thomask77/nucular-keyboard/Docs/IMG_4991.JPG

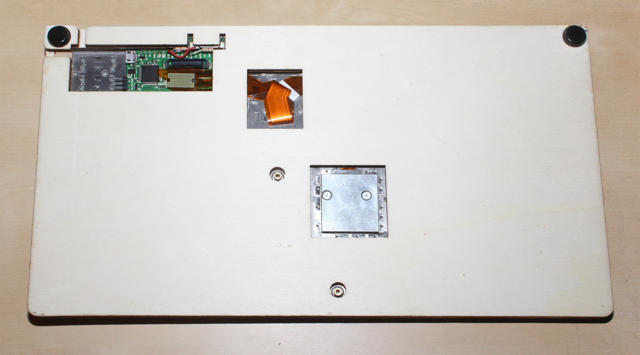
Docs/IMG_4991.JPG
