thomask77/nucular-keyboard/Docs/IMG_4995.JPG

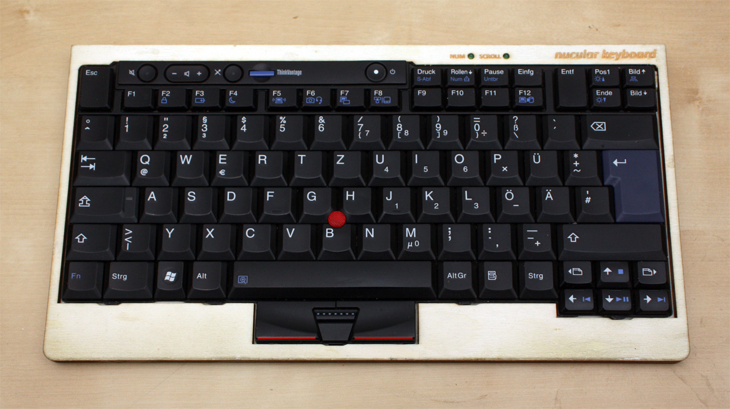
Docs/IMG_4995.JPG
