thomask77/nucular-keyboard/Bootloader/Src/main.c

/**
  ******************************************************************************
  * File Name          : main.c
  * Date               : 08/12/2014 22:01:44
  * Description        : Main program body
  ******************************************************************************
  *
  * COPYRIGHT(c) 2014 STMicroelectronics
  *
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
  ******************************************************************************
  */

/* Includes ------------------------------------------------------------------*/
#include "stm32l0xx_hal.h"
#include "usb_device.h"


/* USER CODE BEGIN 0 */

int check_boot_enter(void)
{
    uint32_t rtc_bkp0r = RTC->BKP0R;

    // clear signature
    //
    RCC->APB1ENR |=  RCC_APB1ENR_PWREN;
    PWR->CR |= PWR_CR_DBP;
    RTC->BKP0R = 0x00000000;
    PWR->CR &= ~PWR_CR_DBP;

    return (rtc_bkp0r == 0xB00710AD) ||
           (!(GPIOC->IDR & GPIO_PIN_14) &&
            !(GPIOB->IDR & GPIO_PIN_9 )  );
}

/* USER CODE END 0 */

void SystemClock_Config(void);
static void MX_GPIO_Init(void);

int main(void)
{

  /* MCU Configuration----------------------------------------------------------*/

  /* Reset of all peripherals, Initializes the Flash interface and the Systick. */
  HAL_Init();

  /* Configure the system clock */
  SystemClock_Config();

  /* System interrupt init*/
  HAL_NVIC_SetPriority(SysTick_IRQn, 0, 0);

  /* Initialize all configured peripherals */
  MX_GPIO_Init();
  MX_USB_DEVICE_Init();

  /* USER CODE BEGIN 2 */

  if (!check_boot_enter())
  {
    void (*JumpToApplication)(void);
    uint32_t JumpAddress;

    /* Test if user code is programmed starting from address 0x08004000 */
    if (((*(__IO uint32_t*)USBD_DFU_APP_DEFAULT_ADD) & 0x2FFE0000 ) == 0x20000000)
    {
      /* Jump to user application */
      JumpAddress = *(__IO uint32_t*) (USBD_DFU_APP_DEFAULT_ADD + 4);
      JumpToApplication = (void*)JumpAddress;

      /* Initialize user application's Stack Pointer */
      __set_MSP(*(__IO uint32_t*) USBD_DFU_APP_DEFAULT_ADD);
      JumpToApplication();
    }
  }

  /* USER CODE END 2 */

  /* USER CODE BEGIN 3 */
  /* Infinite loop */
  while (1)
  {

  }
  /* USER CODE END 3 */

}

/** System Clock Configuration
*/
void SystemClock_Config(void)
{

  RCC_CRSInitTypeDef RCC_CRSInitStruct;
  RCC_ClkInitTypeDef RCC_ClkInitStruct;
  RCC_PeriphCLKInitTypeDef PeriphClkInit;
  RCC_OscInitTypeDef RCC_OscInitStruct;

  __PWR_CLK_ENABLE();

  __HAL_PWR_VOLTAGESCALING_CONFIG(PWR_REGULATOR_VOLTAGE_SCALE1);

  RCC_OscInitStruct.OscillatorType = RCC_OSCILLATORTYPE_HSI|RCC_OSCILLATORTYPE_HSI48;
  RCC_OscInitStruct.HSIState = RCC_HSI_ON;
  RCC_OscInitStruct.HSICalibrationValue = 16;
  RCC_OscInitStruct.HSI48State = RCC_HSI48_ON;
  RCC_OscInitStruct.PLL.PLLState = RCC_PLL_ON;
  RCC_OscInitStruct.PLL.PLLSource = RCC_PLLSOURCE_HSI;
  RCC_OscInitStruct.PLL.PLLMUL = RCC_PLLMUL_4;
  RCC_OscInitStruct.PLL.PLLDIV = RCC_PLLDIV_2;
  HAL_RCC_OscConfig(&RCC_OscInitStruct);

  RCC_ClkInitStruct.ClockType = RCC_CLOCKTYPE_SYSCLK;
  RCC_ClkInitStruct.SYSCLKSource = RCC_SYSCLKSOURCE_PLLCLK;
  RCC_ClkInitStruct.AHBCLKDivider = RCC_SYSCLK_DIV1;
  RCC_ClkInitStruct.APB1CLKDivider = RCC_HCLK_DIV1;
  RCC_ClkInitStruct.APB2CLKDivider = RCC_HCLK_DIV1;
  HAL_RCC_ClockConfig(&RCC_ClkInitStruct, FLASH_LATENCY_1);

  PeriphClkInit.PeriphClockSelection = RCC_PERIPHCLK_USB;
  PeriphClkInit.UsbClockSelection = RCC_USBCLKSOURCE_HSI48;
  HAL_RCCEx_PeriphCLKConfig(&PeriphClkInit);

  __SYSCFG_CLK_ENABLE();

  __CRS_CLK_ENABLE();

  RCC_CRSInitStruct.Prescaler = RCC_CRS_SYNC_DIV1;
  RCC_CRSInitStruct.Source = RCC_CRS_SYNC_SOURCE_USB;
  RCC_CRSInitStruct.Polarity = RCC_CRS_SYNC_POLARITY_RISING;
  RCC_CRSInitStruct.ReloadValue = __HAL_RCC_CRS_CALCULATE_RELOADVALUE(48000000,1000);
  RCC_CRSInitStruct.ErrorLimitValue = 34;
  RCC_CRSInitStruct.HSI48CalibrationValue = 32;
  HAL_RCCEx_CRSConfig(&RCC_CRSInitStruct);

}

/** Configure pins as 
        * Analog 
        * Input 
        * Output
        * EVENT_OUT
        * EXTI
*/
void MX_GPIO_Init(void)
{

  GPIO_InitTypeDef GPIO_InitStruct;

  /* GPIO Ports Clock Enable */
  __GPIOC_CLK_ENABLE();
  __GPIOA_CLK_ENABLE();
  __GPIOB_CLK_ENABLE();

  /*Configure GPIO pin : PC14 */
  GPIO_InitStruct.Pin = GPIO_PIN_14;
  GPIO_InitStruct.Mode = GPIO_MODE_INPUT;
  GPIO_InitStruct.Pull = GPIO_PULLUP;
  HAL_GPIO_Init(GPIOC, &GPIO_InitStruct);

  /*Configure GPIO pin : PB9 */
  GPIO_InitStruct.Pin = GPIO_PIN_9;
  GPIO_InitStruct.Mode = GPIO_MODE_INPUT;
  GPIO_InitStruct.Pull = GPIO_PULLUP;
  HAL_GPIO_Init(GPIOB, &GPIO_InitStruct);

}

#ifdef USE_FULL_ASSERT

/**
   * @brief Reports the name of the source file and the source line number
   * where the assert_param error has occurred.
   * @param file: pointer to the source file name
   * @param line: assert_param error line source number
   * @retval None
   */
void assert_failed(uint8_t* file, uint32_t line)
{
  /* USER CODE BEGIN 6 */
/* User can add his own implementation to report the file name and line number,
ex: printf("Wrong parameters value: file %s on line %d\r\n", file, line) */
  /* USER CODE END 6 */

}

#endif

/**
  * @}
  */ 

/**
  * @}
*/ 

/************************ (C) COPYRIGHT STMicroelectronics *****END OF FILE****/
