thomask77/nucular-keyboard/Docs/Bootloader.ioc

Mcu.UserName=STM32L052R8Tx
PA11.Signal=USB_DM
PA12.Signal=USB_DP
PA13.Signal=SYS_SWDIO
PA14.Signal=SYS_SWCLK
PB9.GPIO_Label=PWRSWITCH
PB9.Signal=GPIO_Input
PC14-OSC32_IN.GPIO_Label=HOTKEY
PC14-OSC32_IN.Signal=GPIO_Input
